JeJeff/Envoy/Envoy/envoy-pcb-back.png

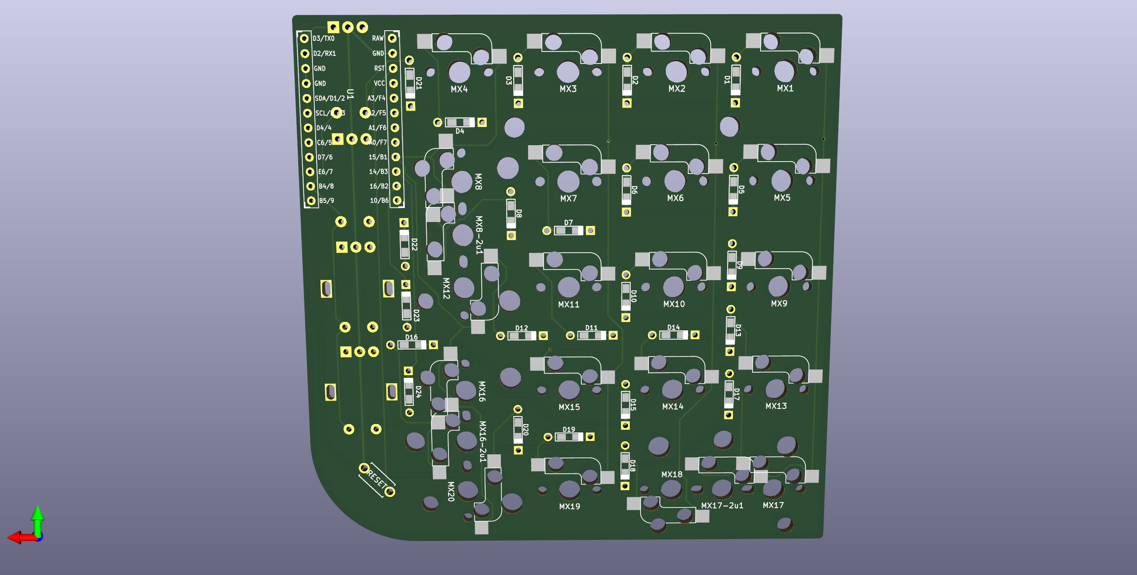
Envoy/envoy-pcb-back.png
