JeJeff/Envoy/Envoy/envoy-pcb-front.png

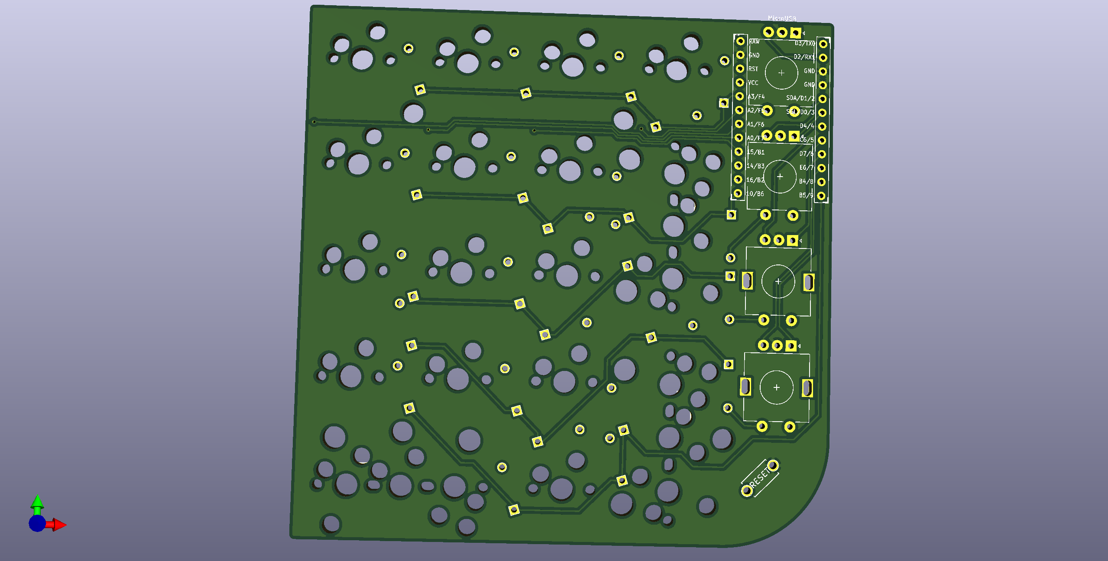
Envoy/envoy-pcb-front.png
