JeJeff/Envoy/images/photos/backplate-front.jpg

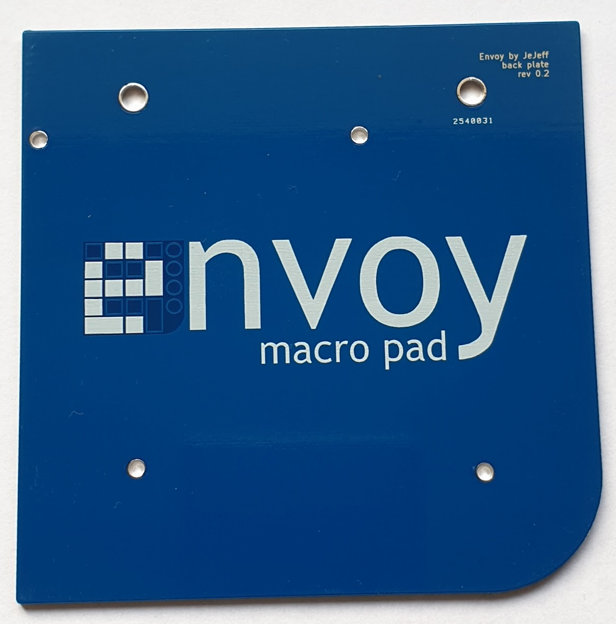
images/photos/backplate-front.jpg
