JeJeff/Envoy/images/photos/pcb-front.jpg

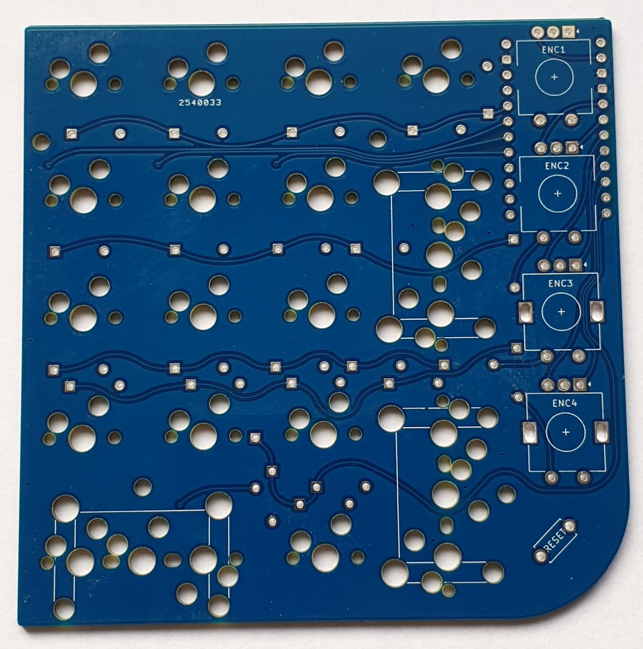
images/photos/pcb-front.jpg
