JeJeff/Envoy/images/flash-guide/qmk-toolbox-preflash.png

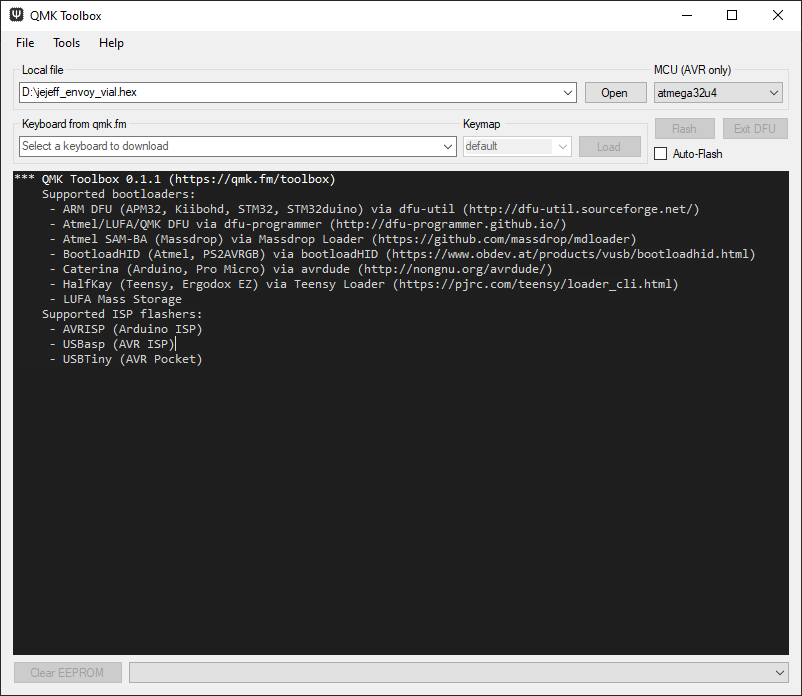
images/flash-guide/qmk-toolbox-preflash.png
